spaceengineer56/bioregenerative-life-support-system-for-mars-missions/images/2.png

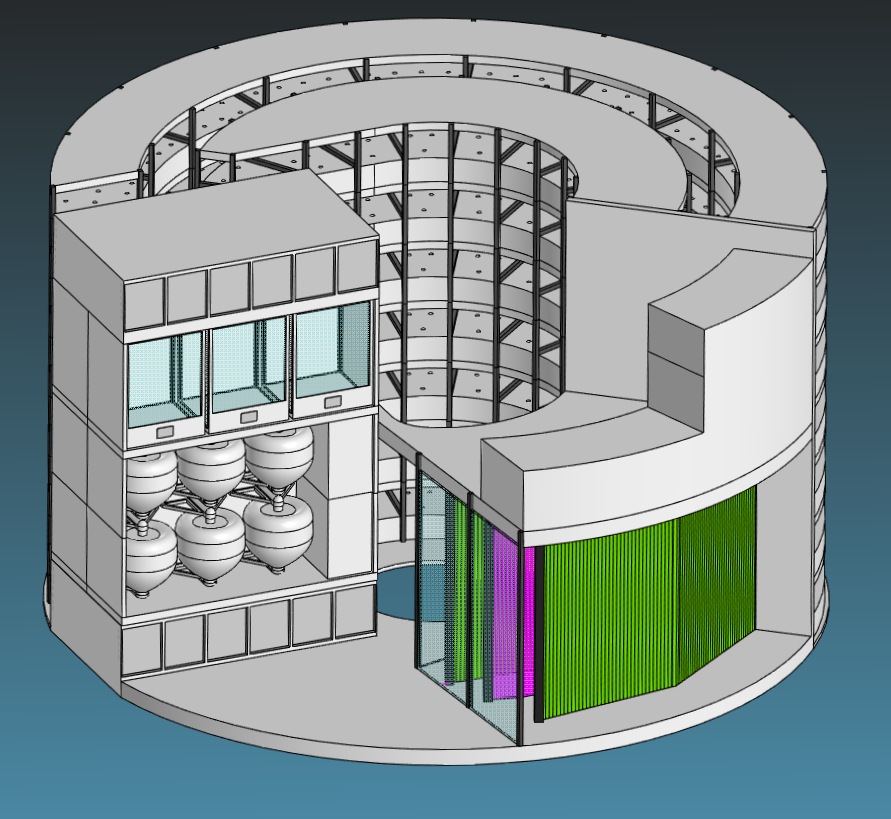
images/2.png
