spaceengineer56/bioregenerative-life-support-system-for-mars-missions/images/20260227_205144.png

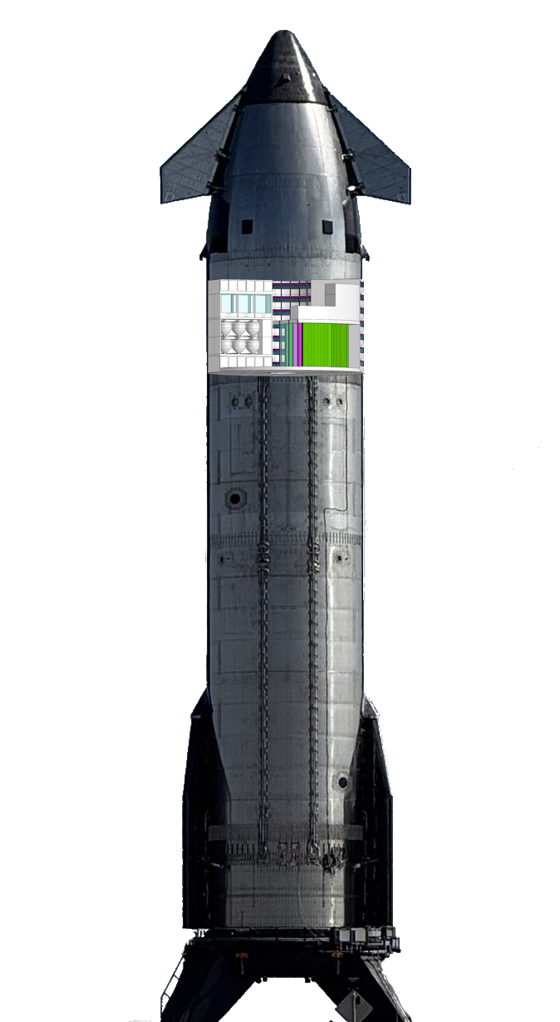
images/20260227_205144.png
