spaceengineer56/bioregenerative-life-support-system-for-mars-missions/images/bottom_view.png

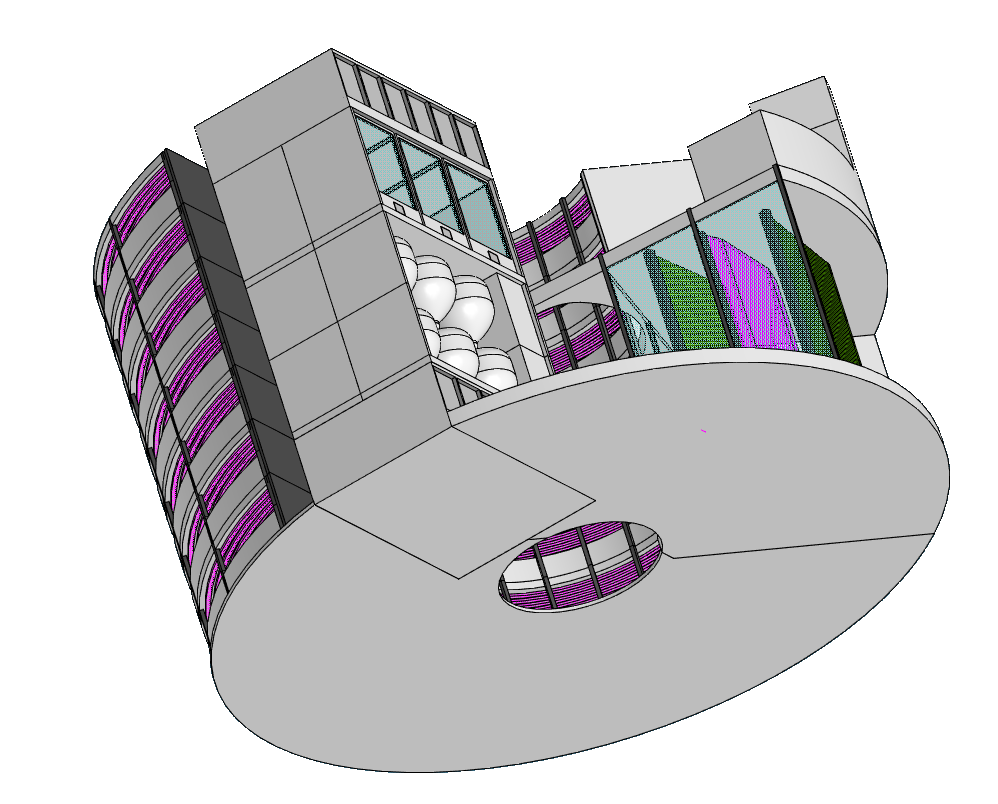
images/bottom_view.png
