spaceengineer56/bioregenerative-life-support-system-for-mars-missions/images/M2TuXAAuvBymV3e3ywjy3Q-2376394809.jpg

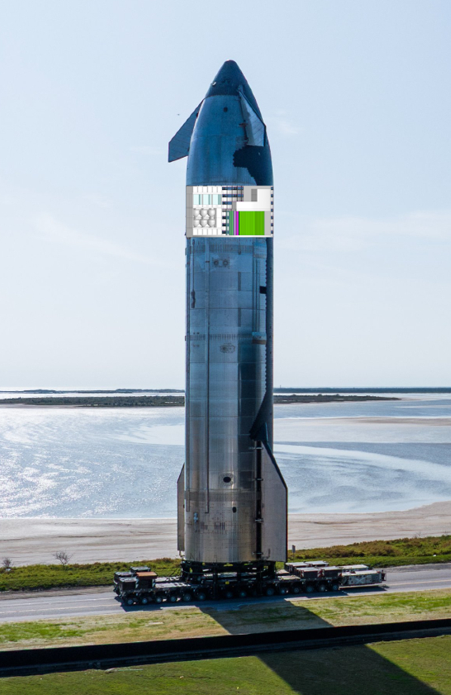
images/M2TuXAAuvBymV3e3ywjy3Q-2376394809.jpg
