spaceengineer56/bioregenerative-life-support-system-for-mars-missions/images/photo_2025-11-06_15-48-50.jpg

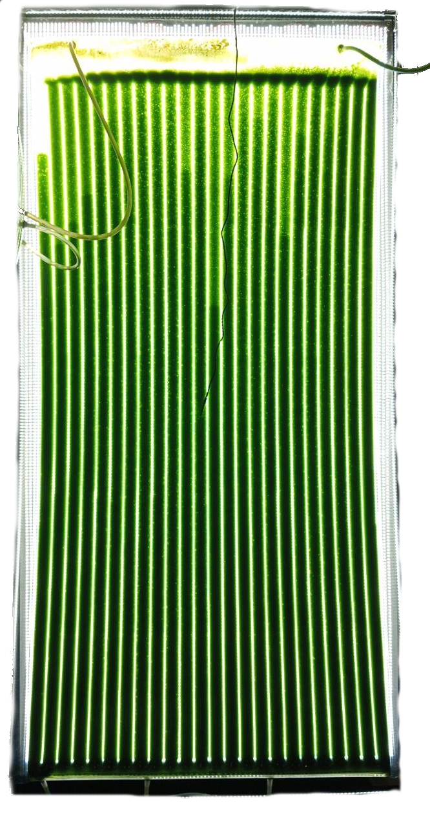
images/photo_2025-11-06_15-48-50.jpg
