spaceengineer56/bioregenerative-life-support-system-for-mars-missions/images/photo_2026-03-13_17-22-31.jpg

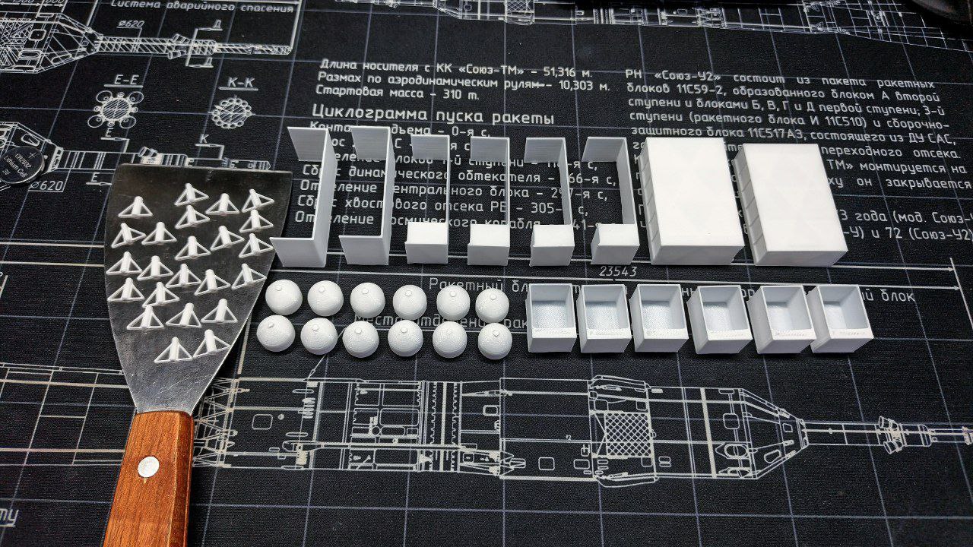
images/photo_2026-03-13_17-22-31.jpg
