spaceengineer56/bioregenerative-life-support-system-for-mars-missions/images/photo_2026-03-14_20-45-20.jpg

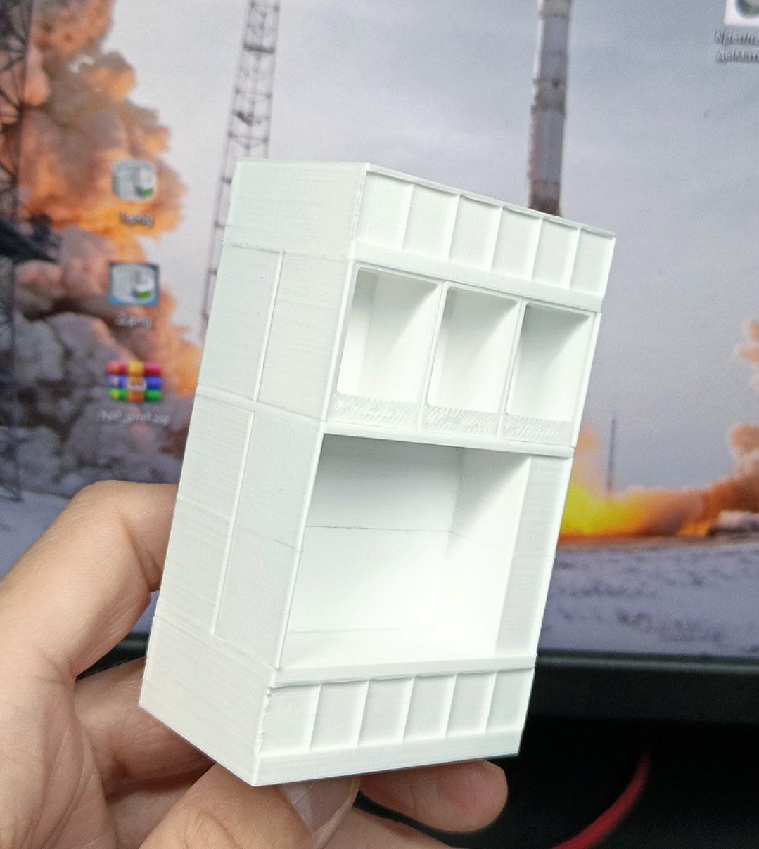
images/photo_2026-03-14_20-45-20.jpg
