spaceengineer56/bioregenerative-life-support-system-for-mars-missions/images/Screenshot_4.png

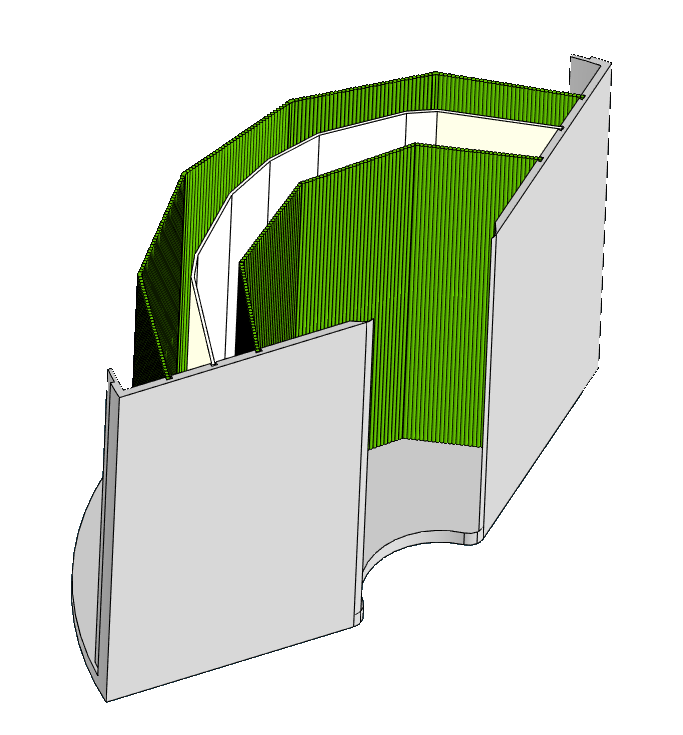
images/Screenshot_4.png
