spaceengineer56/bioregenerative-life-support-system-for-mars-missions/images/Screenshot_6.png

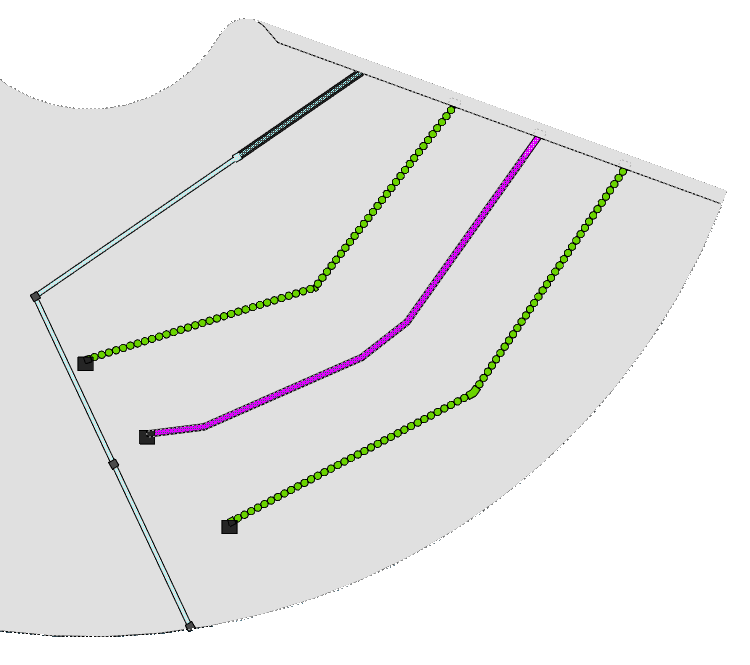
images/Screenshot_6.png
