spaceengineer56/bioregenerative-life-support-system-for-mars-missions/images/Screenshot_8.png

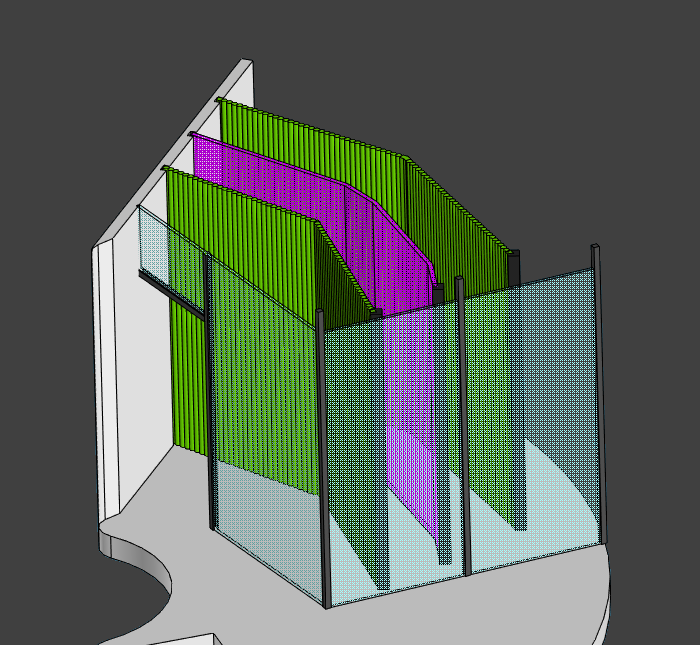
images/Screenshot_8.png
