spaceengineer56/bioregenerative-life-support-system-for-mars-missions/images/Screenshot_9.png

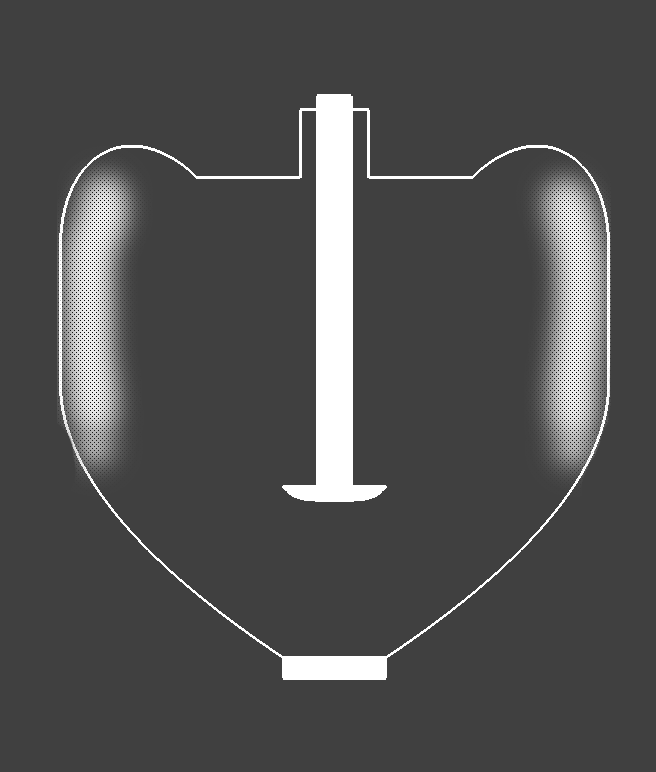
images/Screenshot_9.png
