spaceengineer56/bioregenerative-life-support-system-for-mars-missions/images/Screenshot_11.png

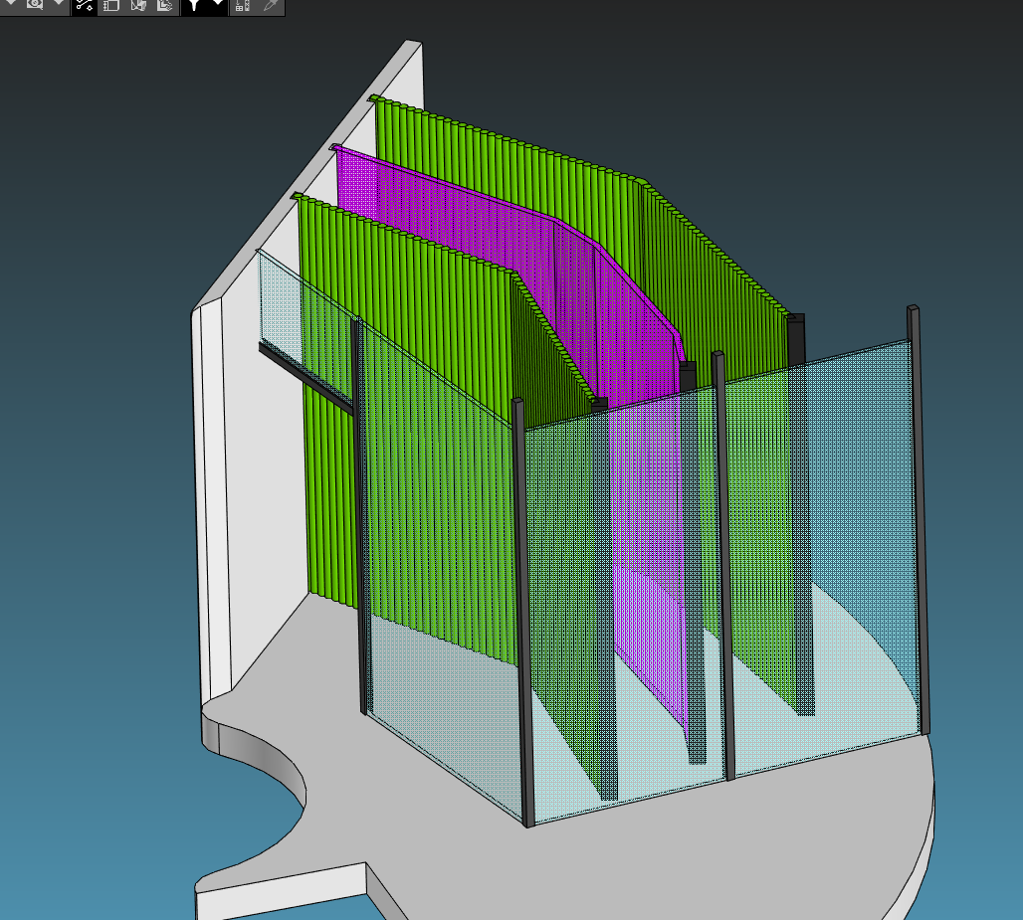
images/Screenshot_11.png
