spaceengineer56/bioregenerative-life-support-system-for-mars-missions/images/Screenshot_12.png

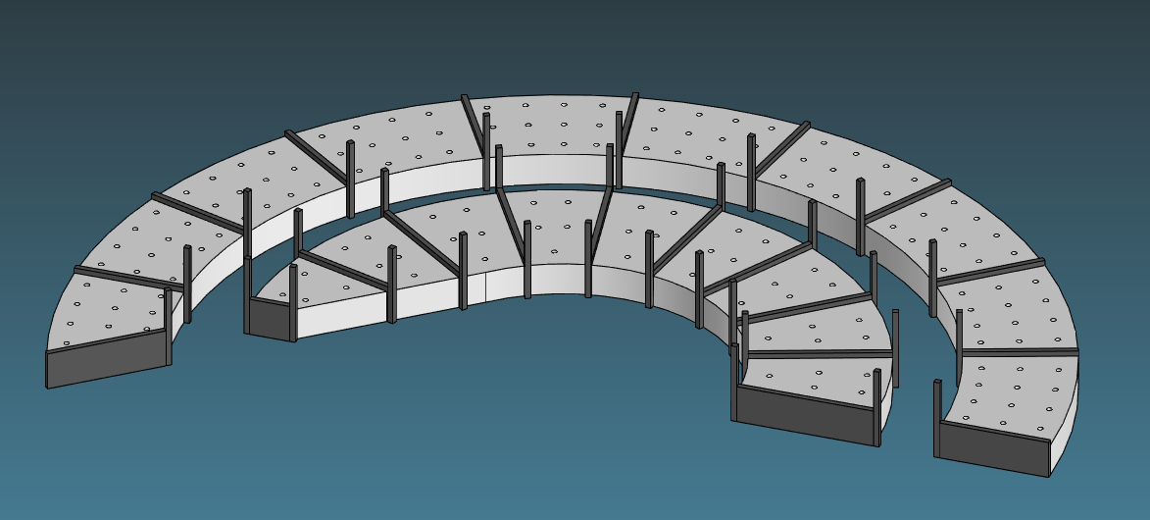
images/Screenshot_12.png
