spaceengineer56/bioregenerative-life-support-system-for-mars-missions/images/Screenshot_13.png

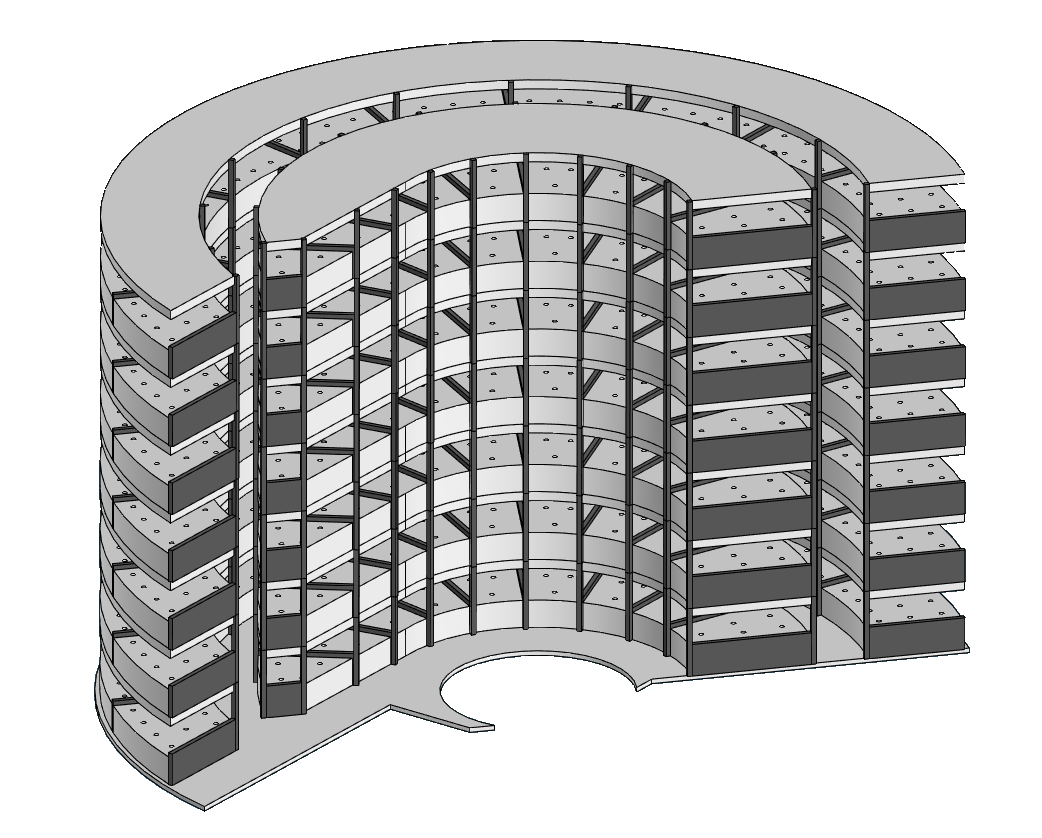
images/Screenshot_13.png
