spaceengineer56/bioregenerative-life-support-system-for-mars-missions/images/Screenshot_14.png

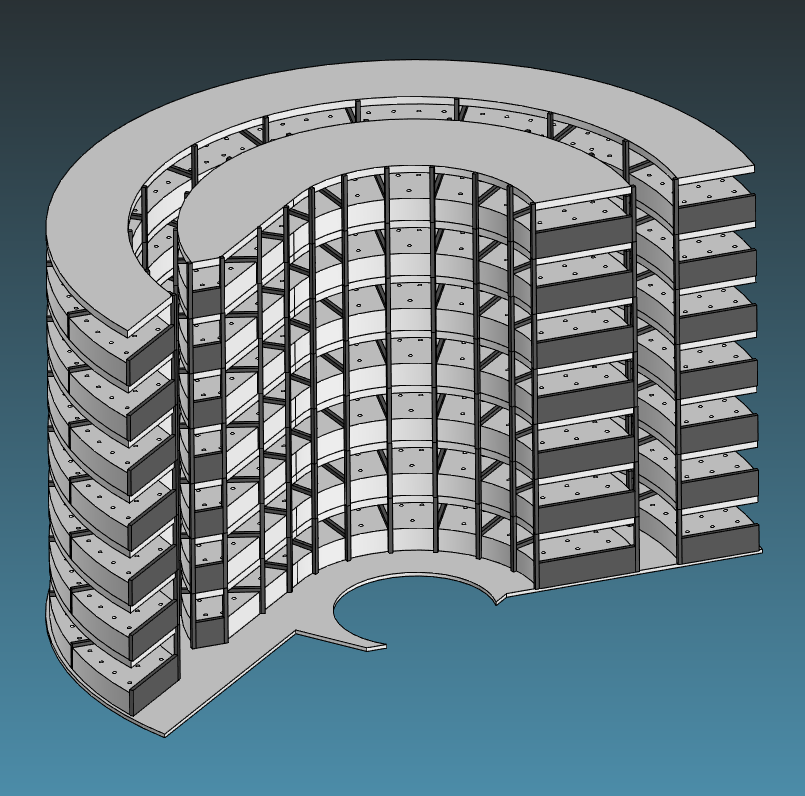
images/Screenshot_14.png
