spaceengineer56/bioregenerative-life-support-system-for-mars-missions/images/Screenshot_15.png

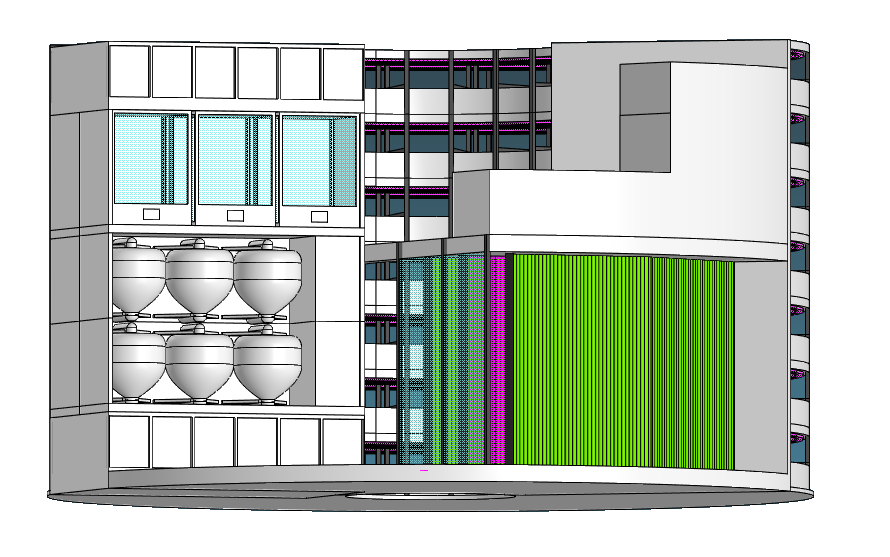
images/Screenshot_15.png
