spaceengineer56/bioregenerative-life-support-system-for-mars-missions/images/starship_mars.jpg

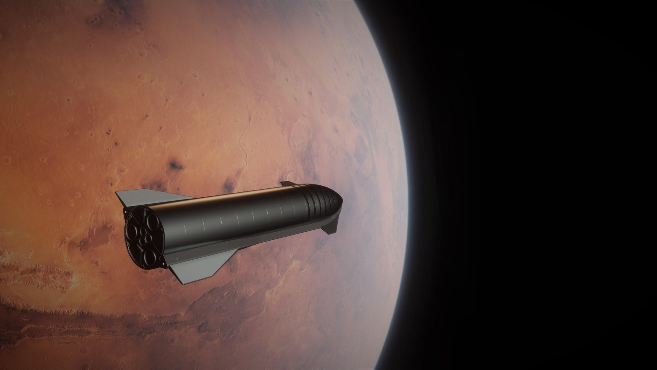
images/starship_mars.jpg
