spaceengineer56/bioregenerative-life-support-system-for-mars-missions/images/trajectory_to_mars.png

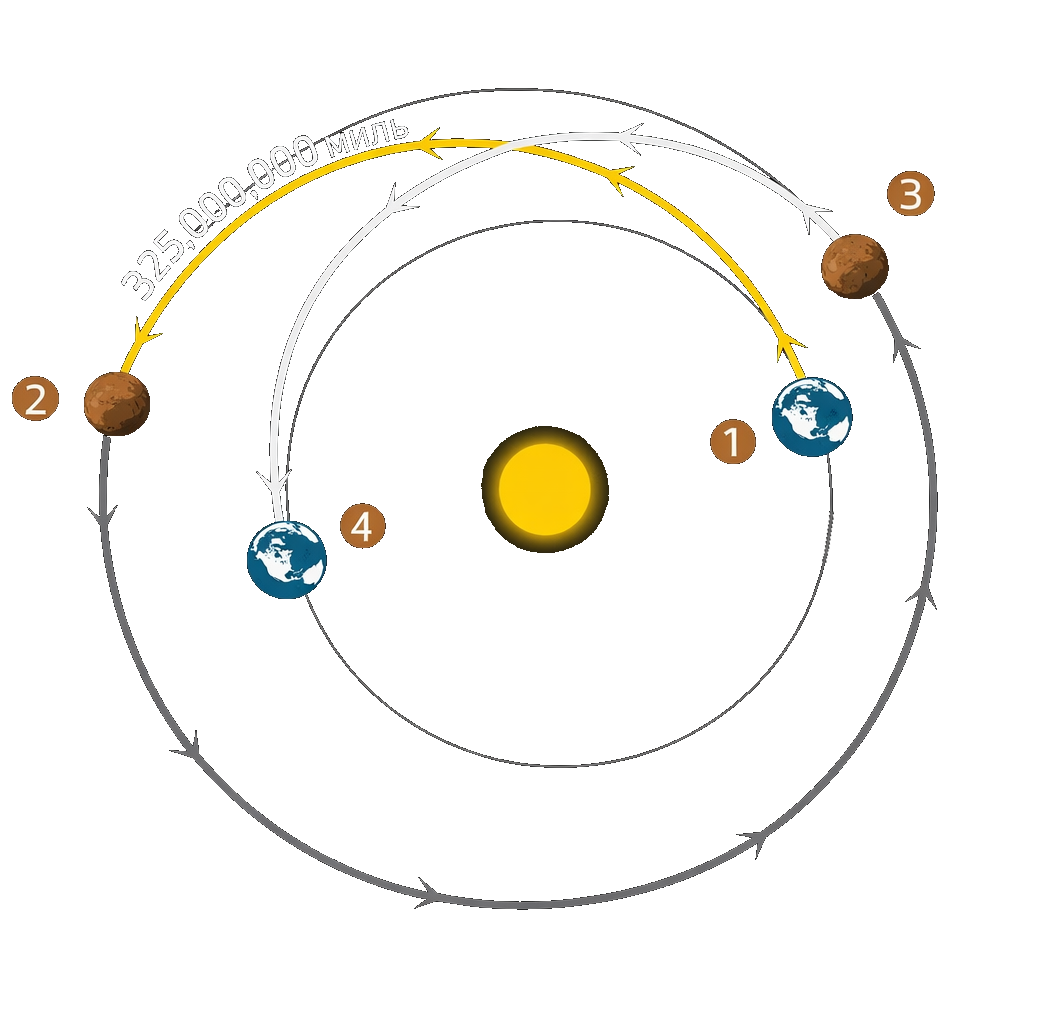
images/trajectory_to_mars.png
