spaceengineer56/bioregenerative-life-support-system-for-mars-missions/images/Рисунок3.png

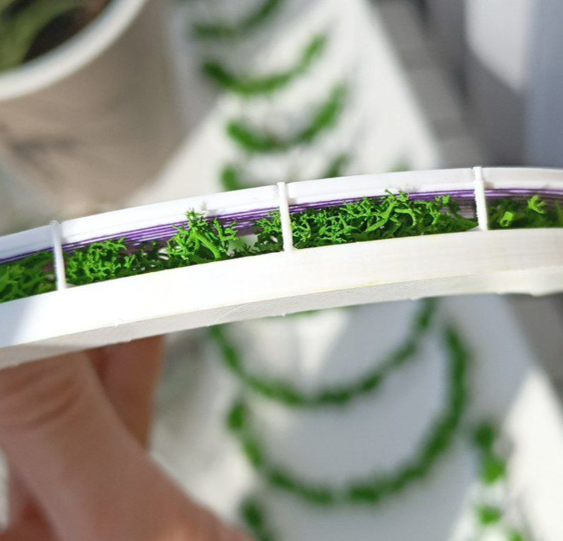
images/Рисунок3.png
