spaceengineer56/bioregenerative-life-support-system-for-mars-missions/images/Рисунок5.png

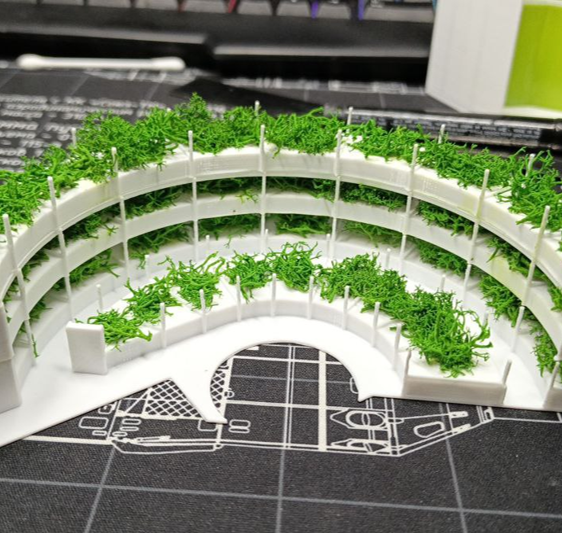
images/Рисунок5.png
