spaceengineer56/bioregenerative-life-support-system-for-mars-missions/references/Актовая речь Синяка Ю.Е. на заседании Ученого Совета, октябрь 2008 г_files/sinak.jpg

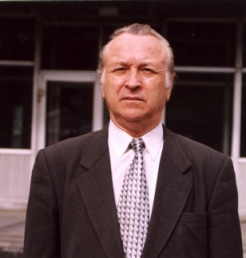
references/Актовая речь Синяка Ю.Е. на заседании Ученого Совета, октябрь 2008 г_files/sinak.jpg
