spaceengineer56/bioregenerative-life-support-system-for-mars-missions/CAD/other/Рабочее место.stl

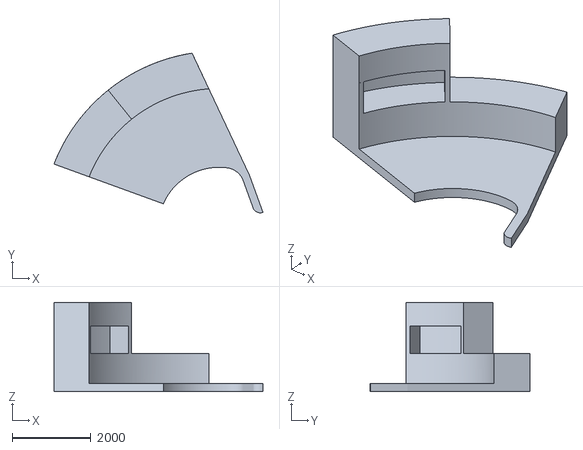
[picture p59: CAD file, 2026-06-27]
CAD/other/Рабочее место.stl
5305.2 x 4054.2 x 2265.0
