spaceengineer56/bioregenerative-life-support-system-for-mars-missions/CAD/aeroponic/Доп опора 2.stl

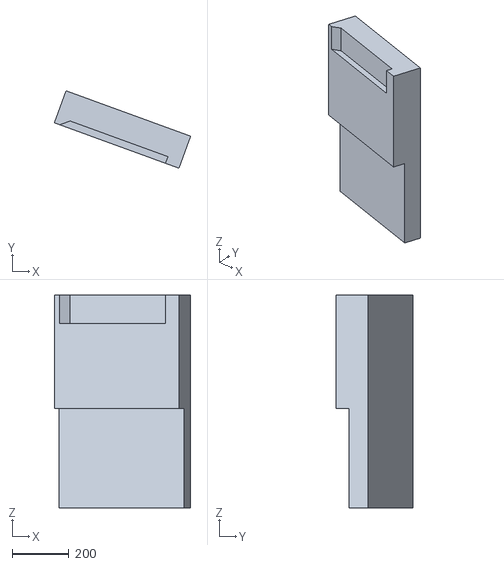
[picture p60: CAD file, 2026-06-27]
CAD/aeroponic/Доп опора 2.stl
480.1 x 272.7 x 750.0
