spaceengineer56/bioregenerative-life-support-system-for-mars-missions/CAD/insects/Дно — толст.stl

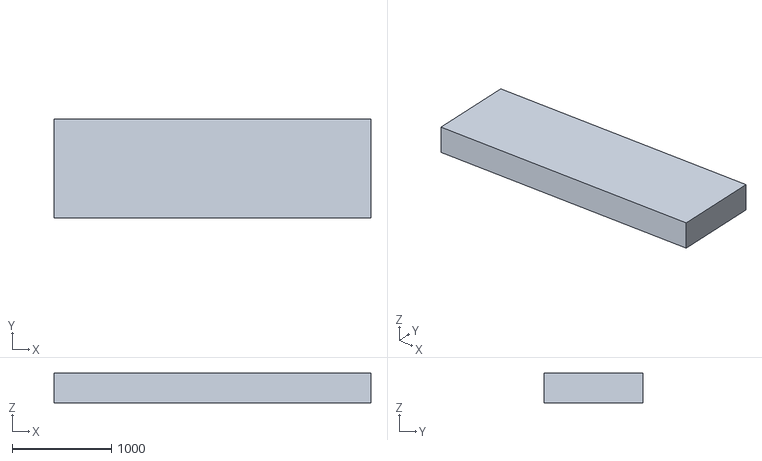
[picture p61: CAD file, 2026-06-27]
CAD/insects/Дно — толст.stl
3200.0 x 998.8 x 300.0
