spaceengineer56/bioregenerative-life-support-system-for-mars-missions/CAD/other/верх платформы.stl

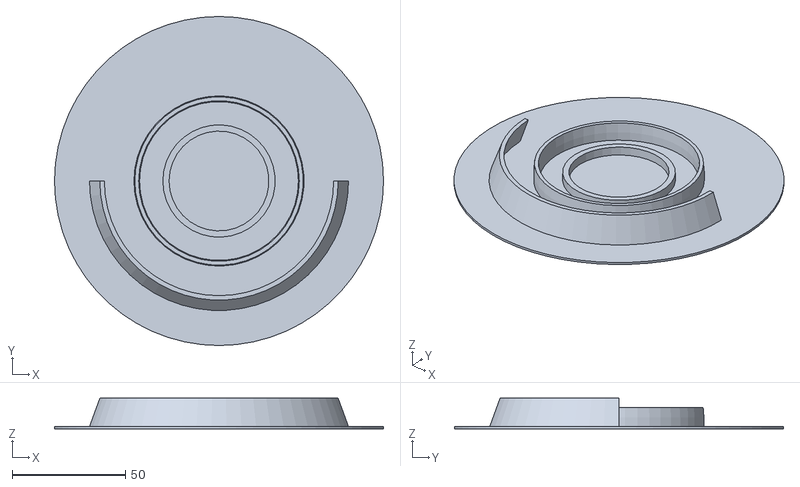
[picture p62: CAD file, 2026-06-27]
CAD/other/верх платформы.stl
145.0 x 145.0 x 13.5
