spaceengineer56/bioregenerative-life-support-system-for-mars-missions/CAD/photobioreactor/Освещение внутр.stl

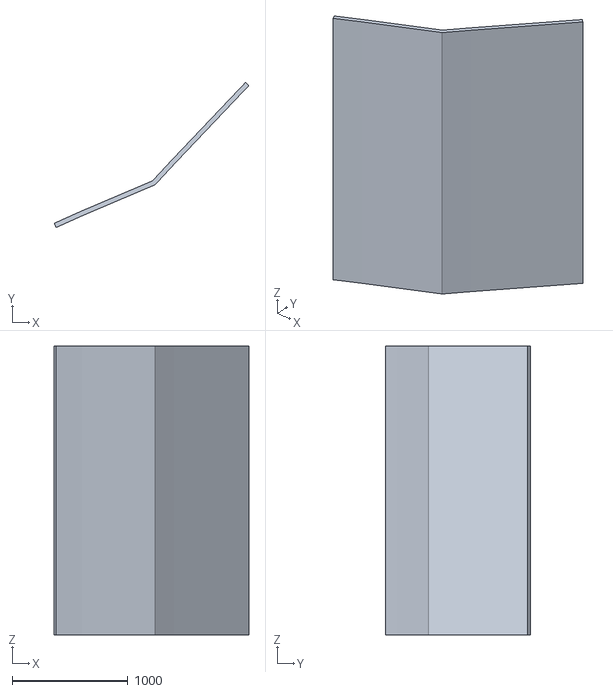
[picture p63: CAD file, 2026-06-27]
CAD/photobioreactor/Освещение внутр.stl
1683.7 x 1254.9 x 2500.0
