spaceengineer56/bioregenerative-life-support-system-for-mars-missions/CAD/aeroponic/Сборка пол с балками и этажом.stl

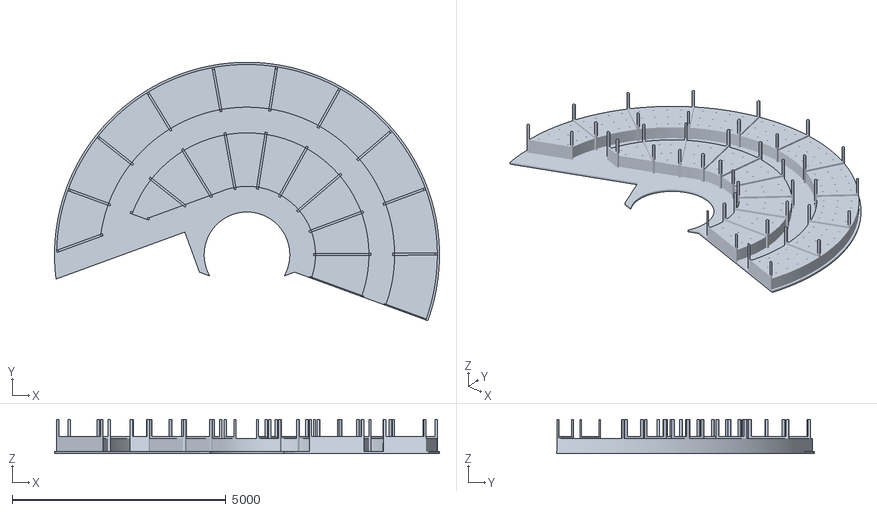
[picture p64: CAD file, 2026-06-27]
CAD/aeroponic/Сборка пол с балками и этажом.stl
9000.5 x 6040.4 x 800.0
