spaceengineer56/bioregenerative-life-support-system-for-mars-missions/CAD/insects/Стенки терр.stl

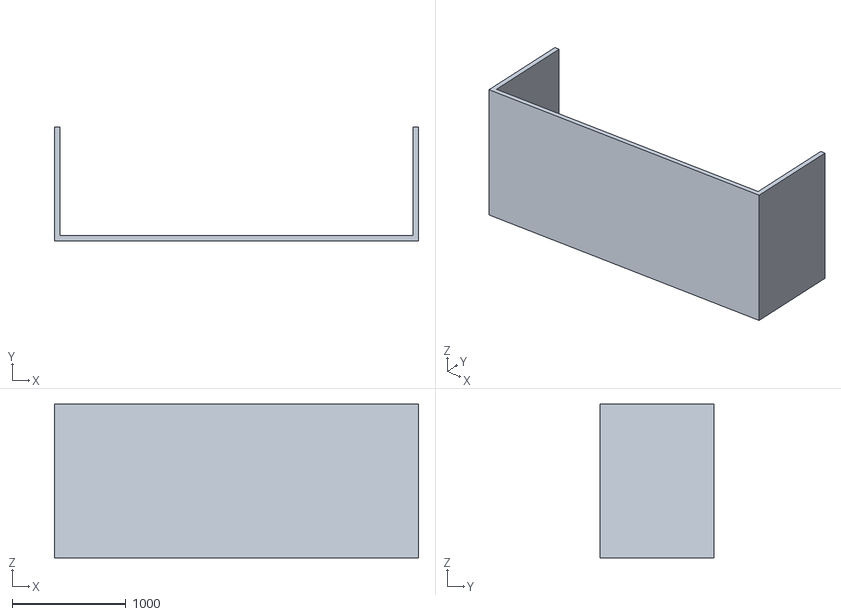
[picture p65: CAD file, 2026-06-27]
CAD/insects/Стенки терр.stl
3200.0 x 998.8 x 1350.0
