spaceengineer56/bioregenerative-life-support-system-for-mars-missions/CAD/photobioreactor/Сегмент_внешн_сегмент.stl

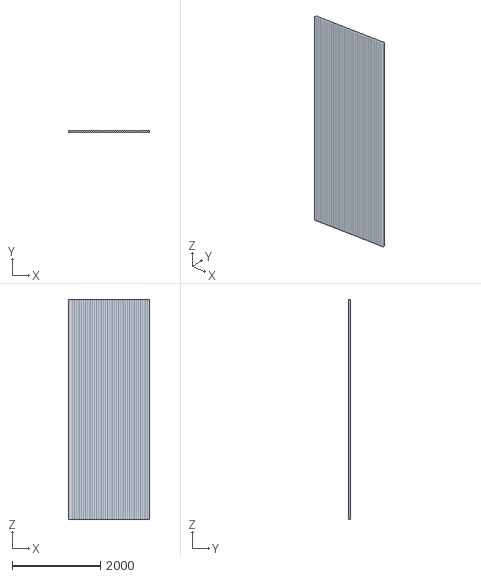
[picture p66: CAD file, 2026-06-27]
CAD/photobioreactor/Сегмент_внешн_сегмент.stl
1850.9 x 50.0 x 5000.0
