spaceengineer56/bioregenerative-life-support-system-for-mars-missions/CAD/insects/Ящики верх.stl

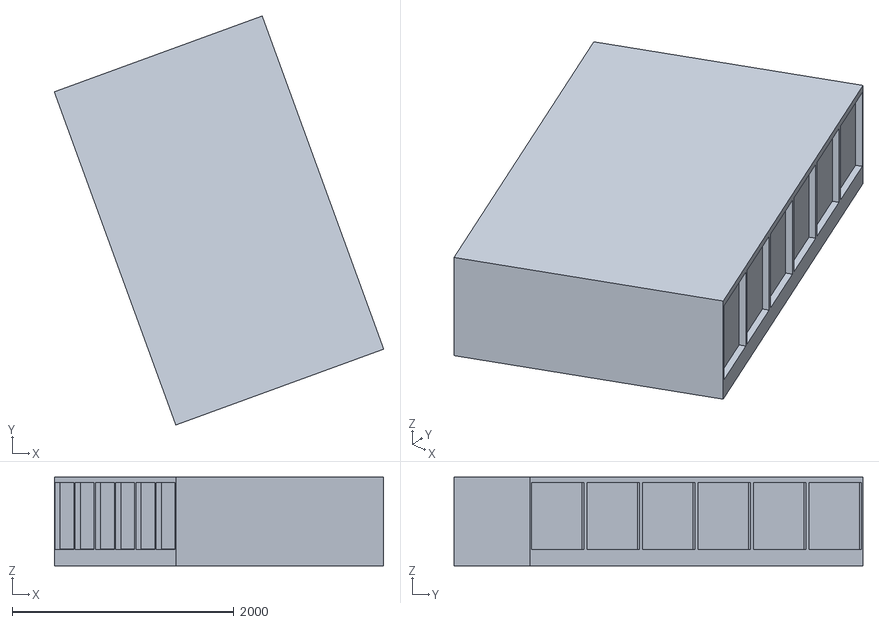
[picture p67: CAD file, 2026-06-27]
CAD/insects/Ящики верх.stl
2973.3 x 3690.8 x 800.0
