spaceengineer56/bioregenerative-life-support-system-for-mars-missions/CAD/photobioreactor/Фотобиореактор_база.stl

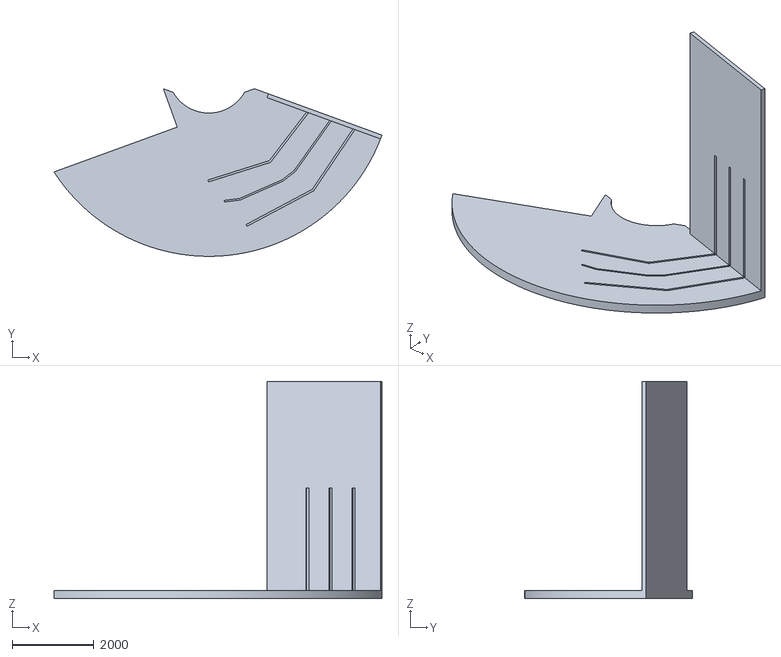
[picture p68: CAD file, 2026-06-27]
CAD/photobioreactor/Фотобиореактор_база.stl
8010.2 x 4094.6 x 5300.0
