spaceengineer56/bioregenerative-life-support-system-for-mars-missions/CAD/insects/Сегмент для личинок.stl

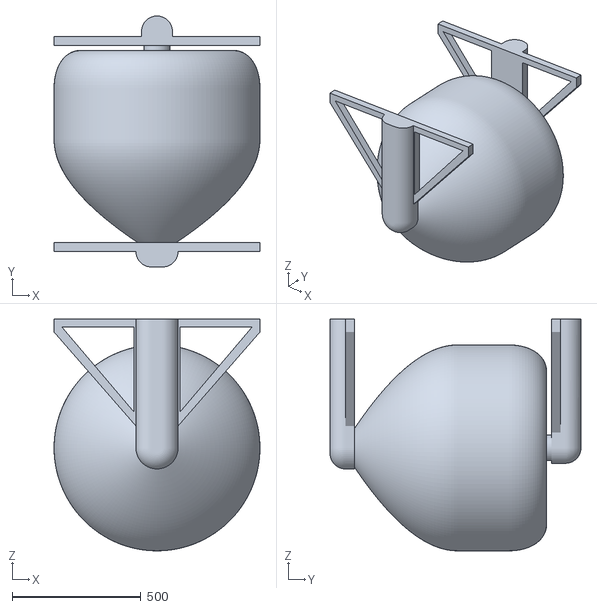
[picture p69: CAD file, 2026-06-27]
CAD/insects/Сегмент для личинок.stl
800.0 x 975.0 x 900.0
