spaceengineer56/bioregenerative-life-support-system-for-mars-missions/CAD/photobioreactor/Слобик остекления мал.stl

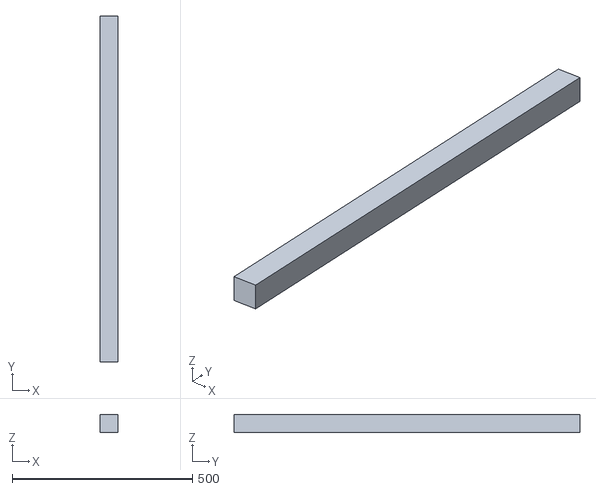
[picture p70: CAD file, 2026-06-27]
CAD/photobioreactor/Слобик остекления мал.stl
50.0 x 960.0 x 50.0
