spaceengineer56/bioregenerative-life-support-system-for-mars-missions/CAD/insects/Переборка между лич и тер.stl

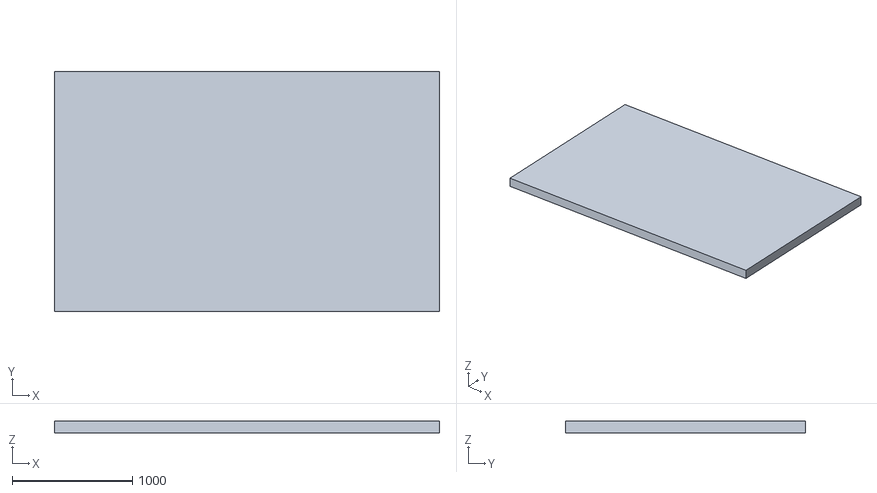
[picture p71: CAD file, 2026-06-27]
CAD/insects/Переборка между лич и тер.stl
3200.0 x 1997.5 x 100.0
