spaceengineer56/bioregenerative-life-support-system-for-mars-missions/CAD/photobioreactor/Освещение правильное.stl

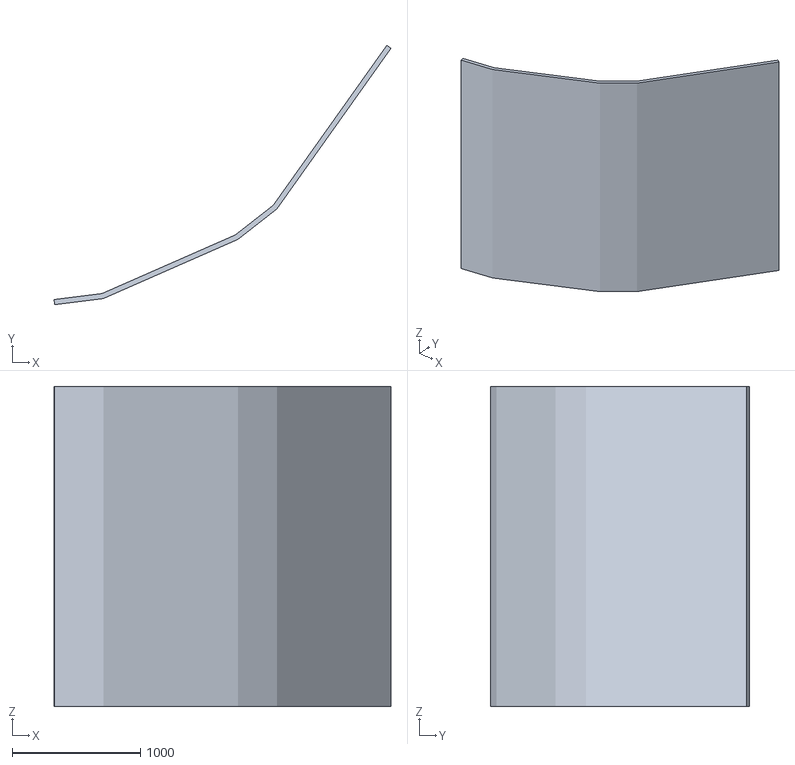
[picture p72: CAD file, 2026-06-27]
CAD/photobioreactor/Освещение правильное.stl
2632.2 x 2025.3 x 2500.0
