spaceengineer56/bioregenerative-life-support-system-for-mars-missions/CAD/insects/Дно ящики.stl

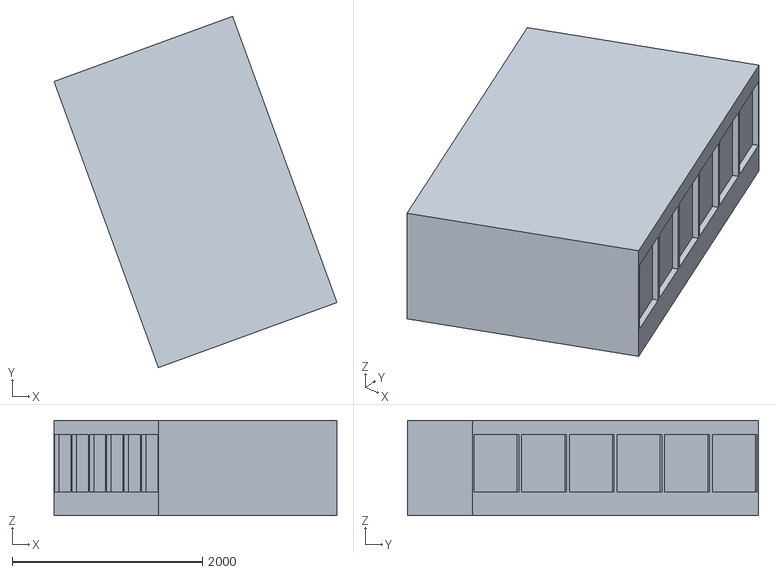
[picture p73: CAD file, 2026-06-27]
CAD/insects/Дно ящики.stl
2973.3 x 3690.8 x 1000.0
