spaceengineer56/bioregenerative-life-support-system-for-mars-missions/CAD/insects/Сегмент для личинок держалка 2.stl

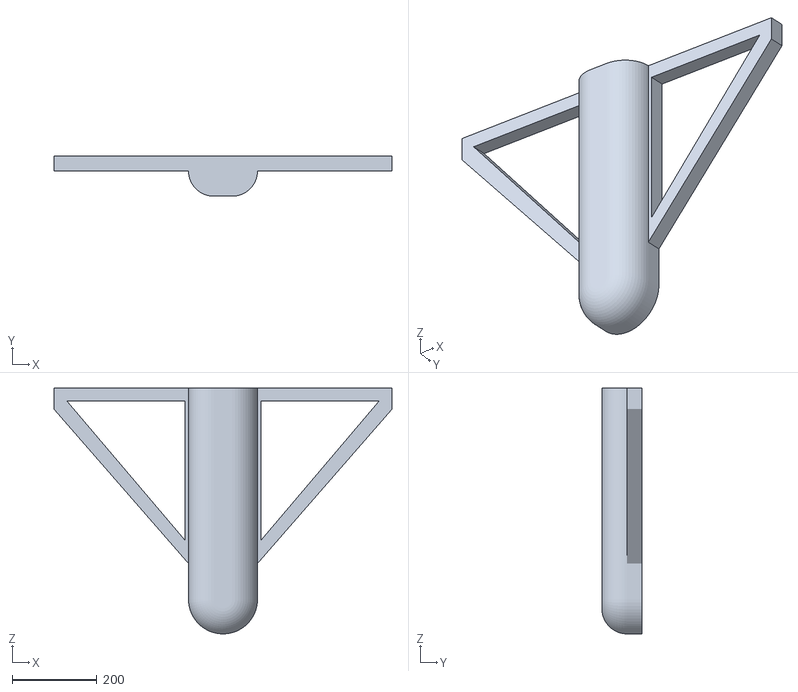
[picture p74: CAD file, 2026-06-27]
CAD/insects/Сегмент для личинок держалка 2.stl
800.0 x 95.6 x 581.8
