spaceengineer56/bioregenerative-life-support-system-for-mars-missions/CAD/insects/Переборка.stl

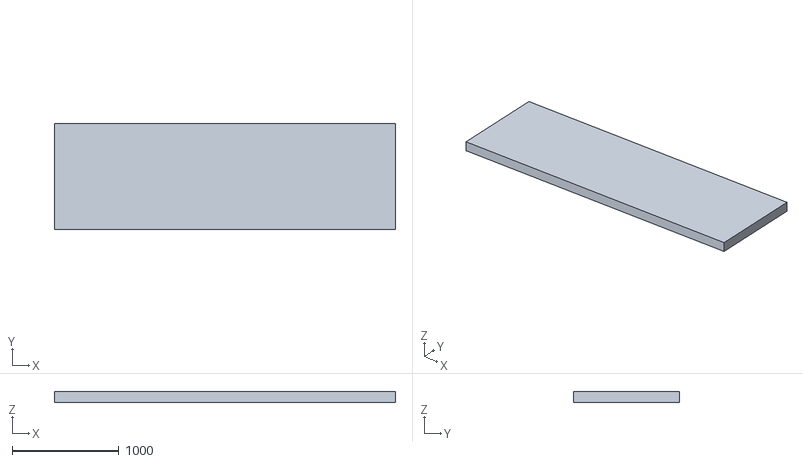
[picture p75: CAD file, 2026-06-27]
CAD/insects/Переборка.stl
3200.0 x 998.8 x 100.0
