spaceengineer56/bioregenerative-life-support-system-for-mars-missions/CAD/insects/Сегмент для личинок цилиндр.stl

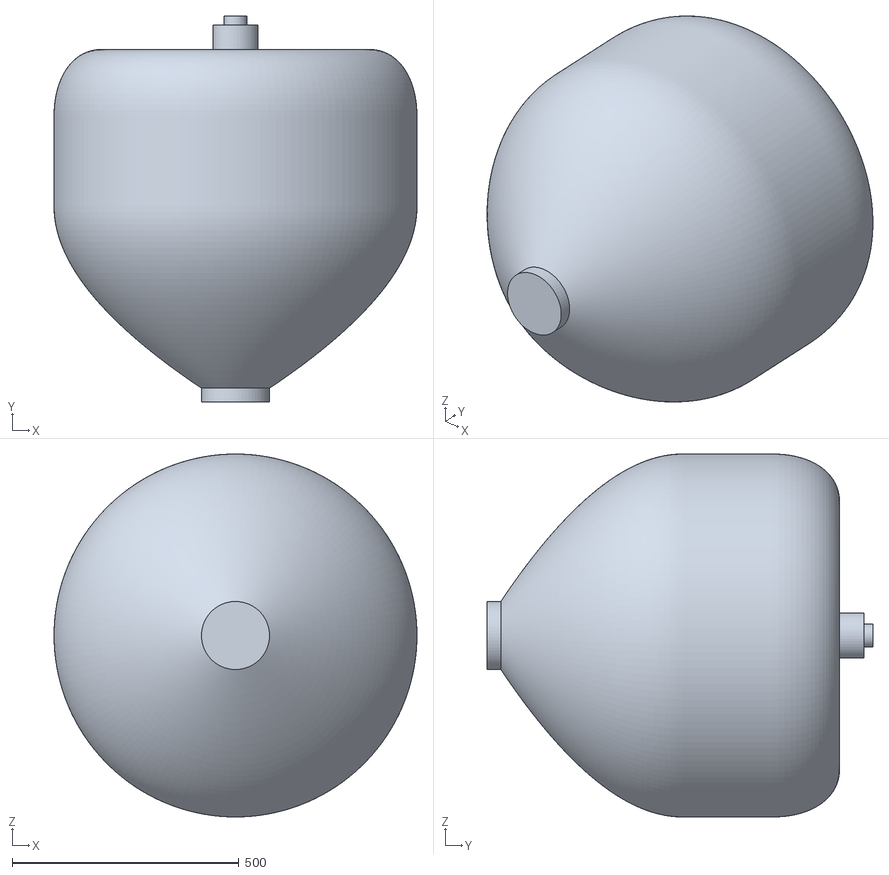
[picture p76: CAD file, 2026-06-27]
CAD/insects/Сегмент для личинок цилиндр.stl
800.0 x 850.0 x 800.0
